plocher/RailroadShield/ControlPointStack-Prototype1.jpg

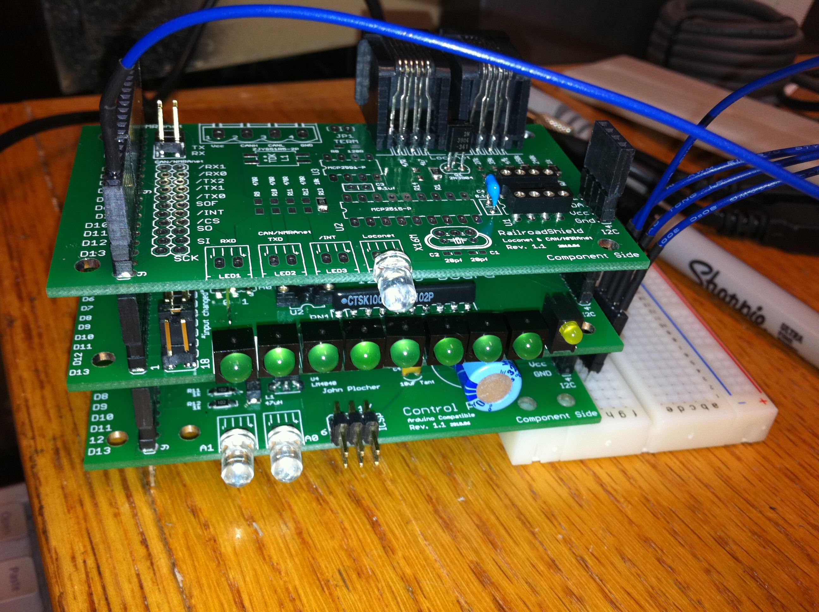
ControlPointStack-Prototype1.jpg
