plocher/RailroadShield/RailroadShield-01.jpg

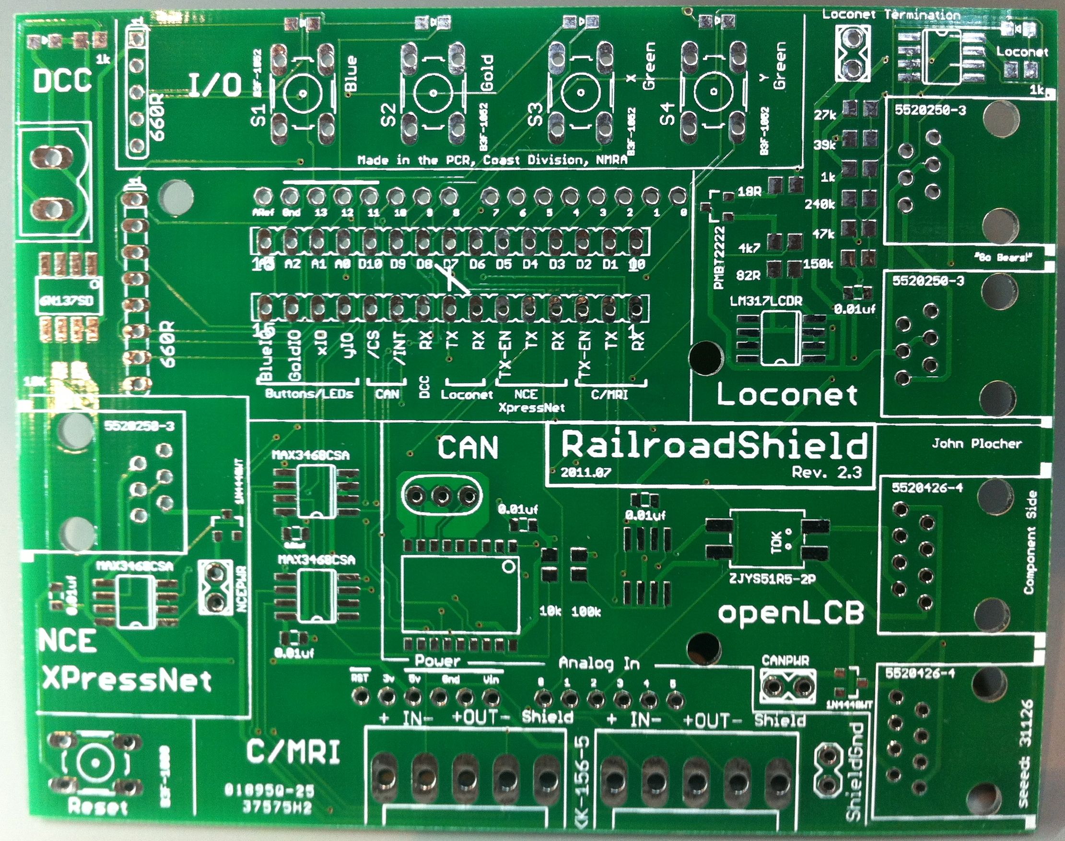
RailroadShield-01.jpg
