plocher/RailroadShield/RailroadShield-02.jpg

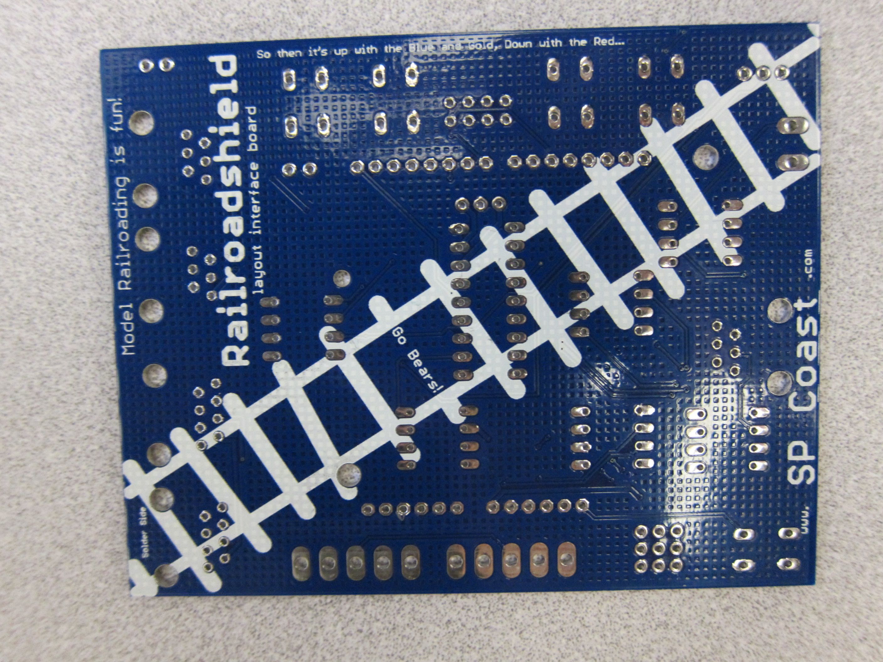
RailroadShield-02.jpg
