plocher/RailroadShield/RailroadShield-04.jpg

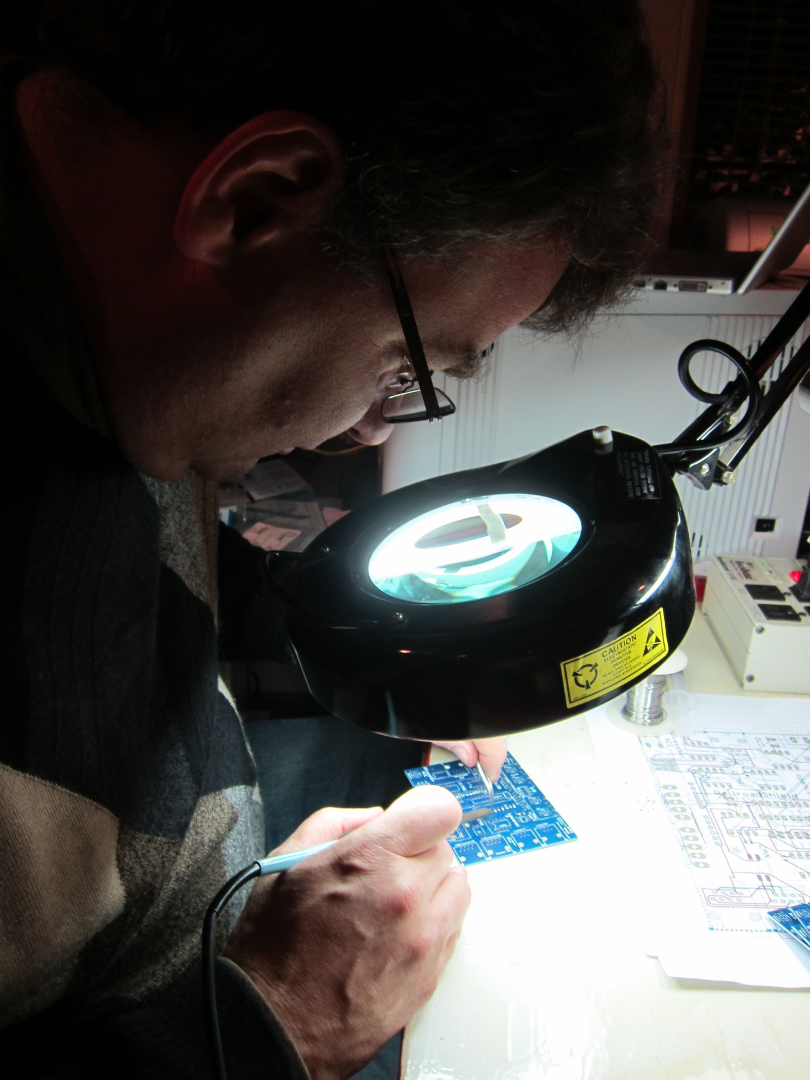
RailroadShield-04.jpg
