plocher/RailroadShield/RailroadShield-05.jpg

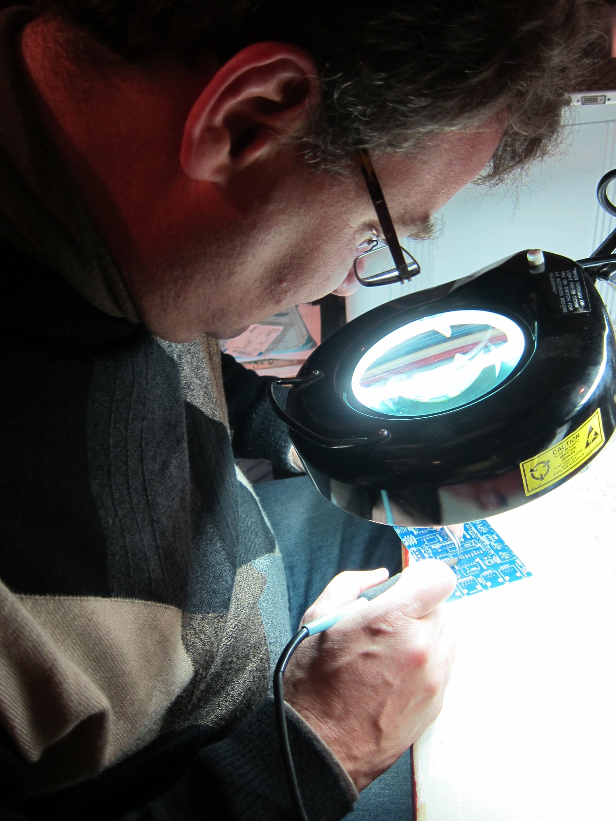
RailroadShield-05.jpg
