plocher/RailroadShield/RailroadShield-07.jpg

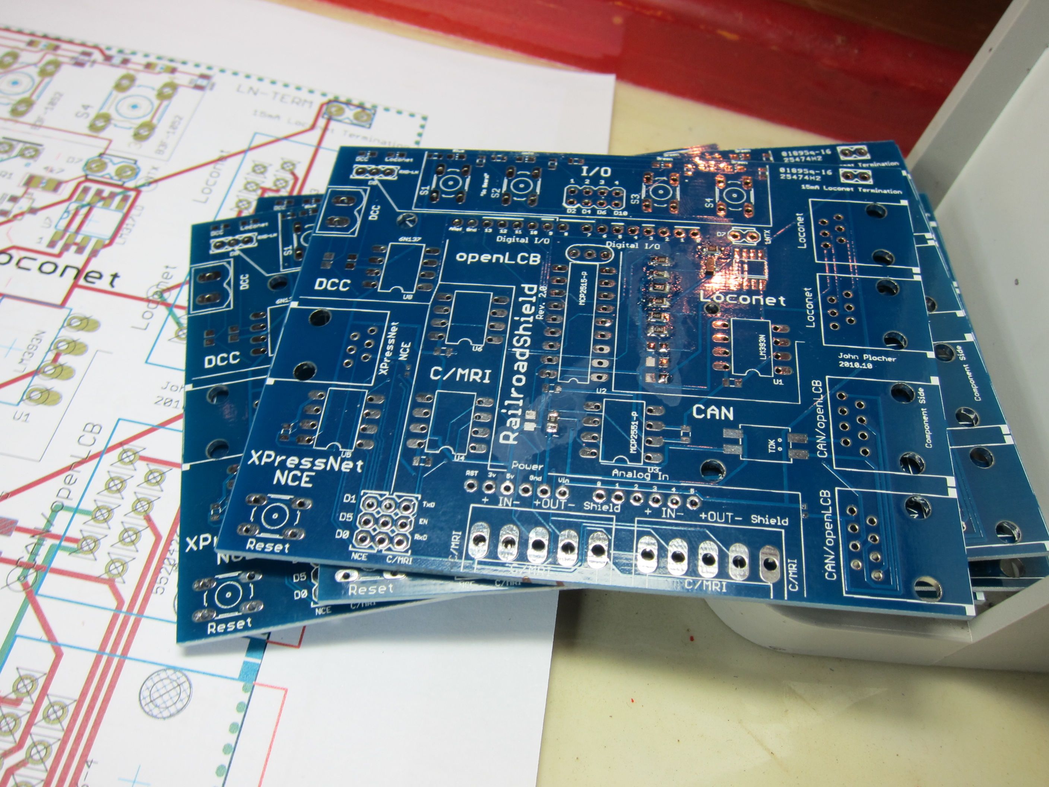
RailroadShield-07.jpg
