plocher/RailroadShield/RailroadShield-10.jpg

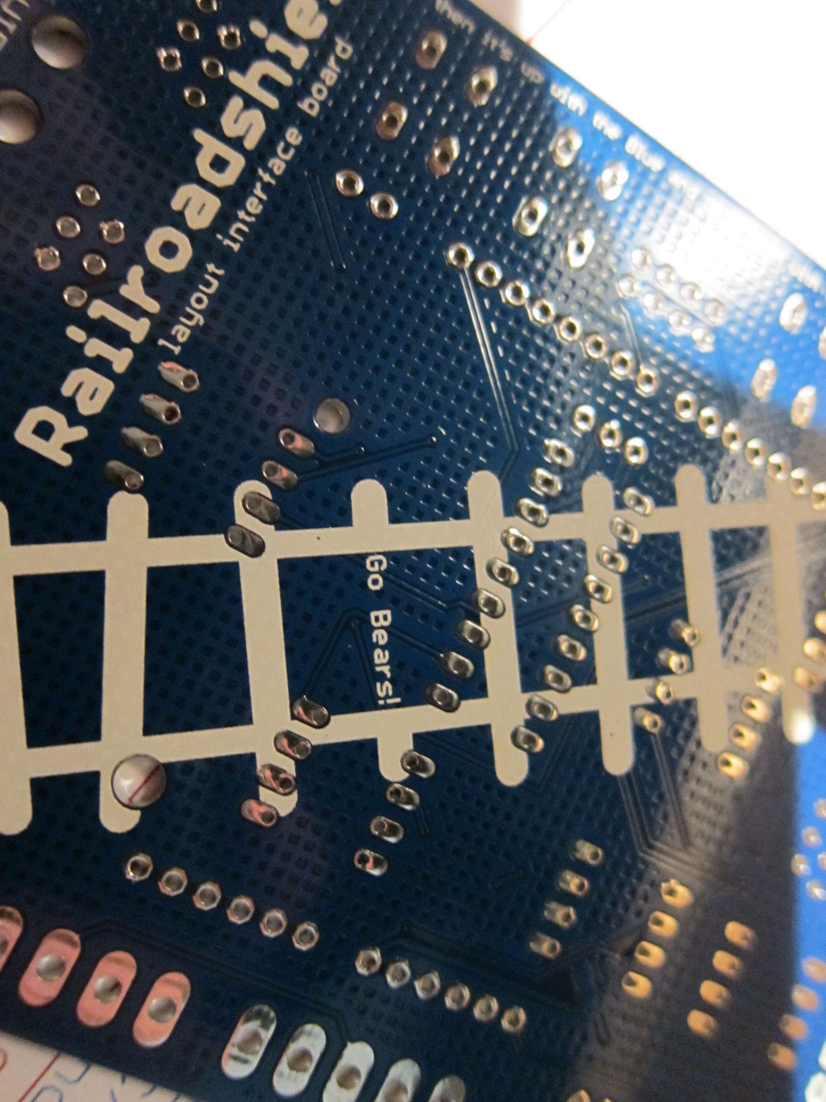
RailroadShield-10.jpg
