plocher/RailroadShield/RailroadShield-12.jpg

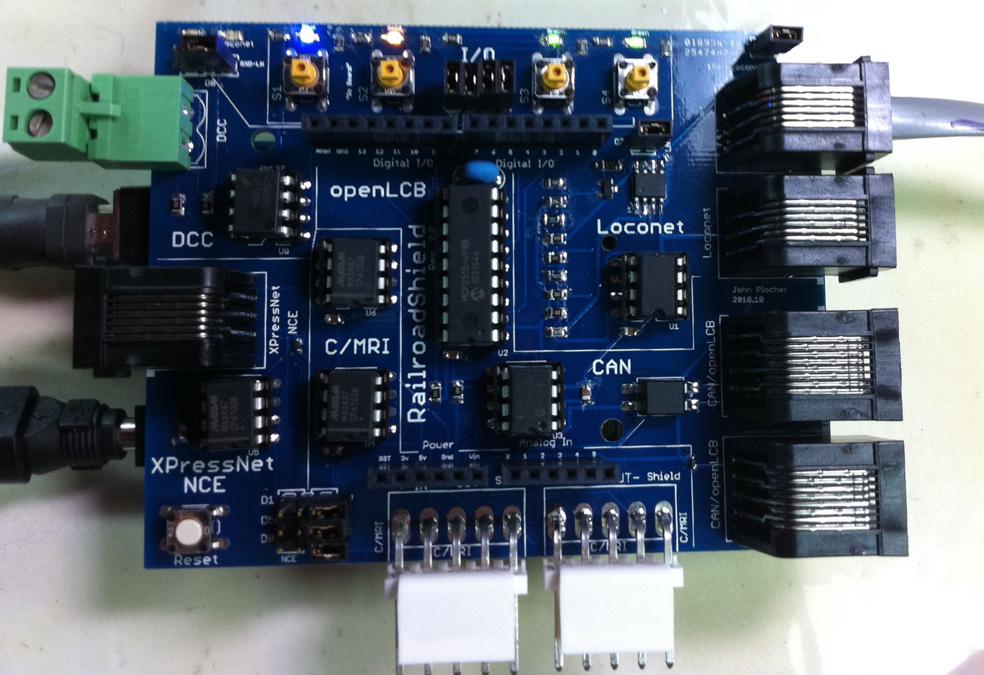
RailroadShield-12.jpg
